pedalboard/pedalboard-hw/3d-models/694106301002 (rev1).stp

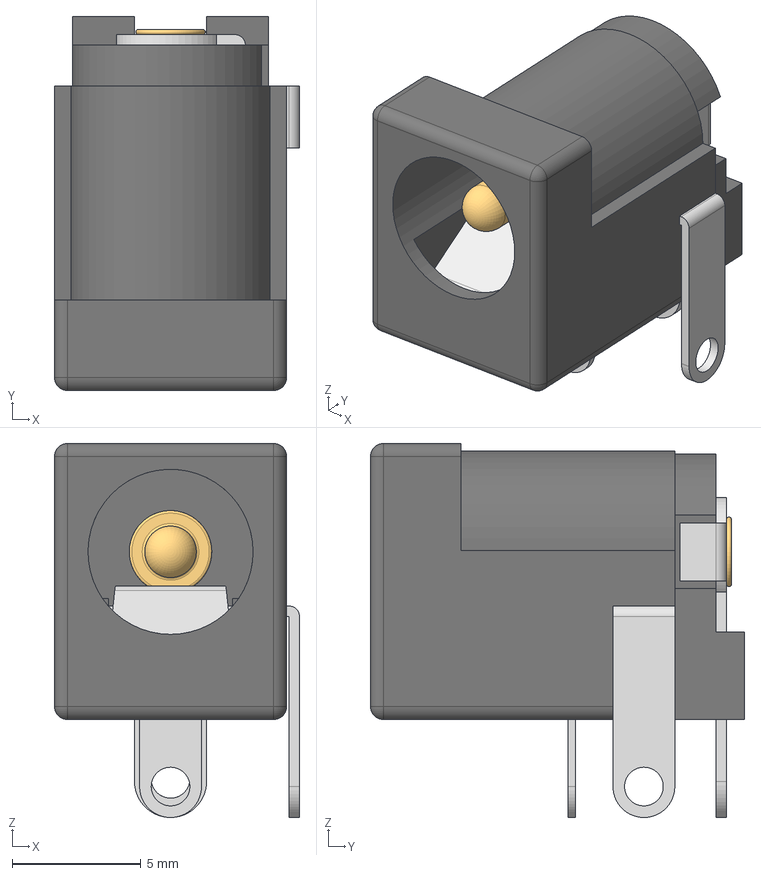
[picture p21: CAD file, 2023-03-27]
3d-models/694106301002 (rev1).stp
9.50 x 14.5 x 14.5 mm
6941xx301002
694106301002_PinContact
6941xx301002_Back
6941xx301002_PinContact2
6941xx301002_PinLame
6941xx301002_PinBis
